UltraFX/Unaeruhr/Unary_1/Unary_1/src/DCF77.h

/*
 * DCF77.h
 *
 * Created: 21.04.2017 23:36:08
 *  Author: Nicolas Dammin
 */ 


#ifndef DCF77_H_
#define DCF77_H_


void dcf77_init(void);
void dcf77_run(void);
void dcf77_timer_handler(void);


#endif /* DCF77_H_ */
