UltraFX/Unaeruhr/Unary_1/Unary_1/src/debounce.h

/*
 * debounce.h
 *
 * Created: 16.09.2015 00:33:18
 *  Author: Nicolas
 */ 


#ifndef DEBOUNCE_H_
#define DEBOUNCE_H_

#define KEY_DDR         DDRD
#define KEY_PORT        PORTD
#define KEY_PIN         PIND
#define KEY0            0
#define KEY1            1
#define KEY2            2
#define ALL_KEYS        (1<<KEY0 | 1<<KEY1 | 1<<KEY2)

#define REPEAT_MASK     (1<<KEY1 | 1<<KEY2)       // repeat: key1, key2
#define REPEAT_START    50                        // after 500ms
#define REPEAT_NEXT     20                        // every 200ms

uint8_t get_key_press( uint8_t key_mask );
uint8_t get_key_rpt( uint8_t key_mask );
uint8_t get_key_short( uint8_t key_mask );
uint8_t get_key_long( uint8_t key_mask );

void initKeys(void);

#endif /* DEBOUNCE_H_ */
